andriykohut/meshtastic-e22-node/hardware/kicad/meshtastic-node.kicad_sch

## KiCad design hardware/kicad/meshtastic-node.kicad_sch (2026-08-19)

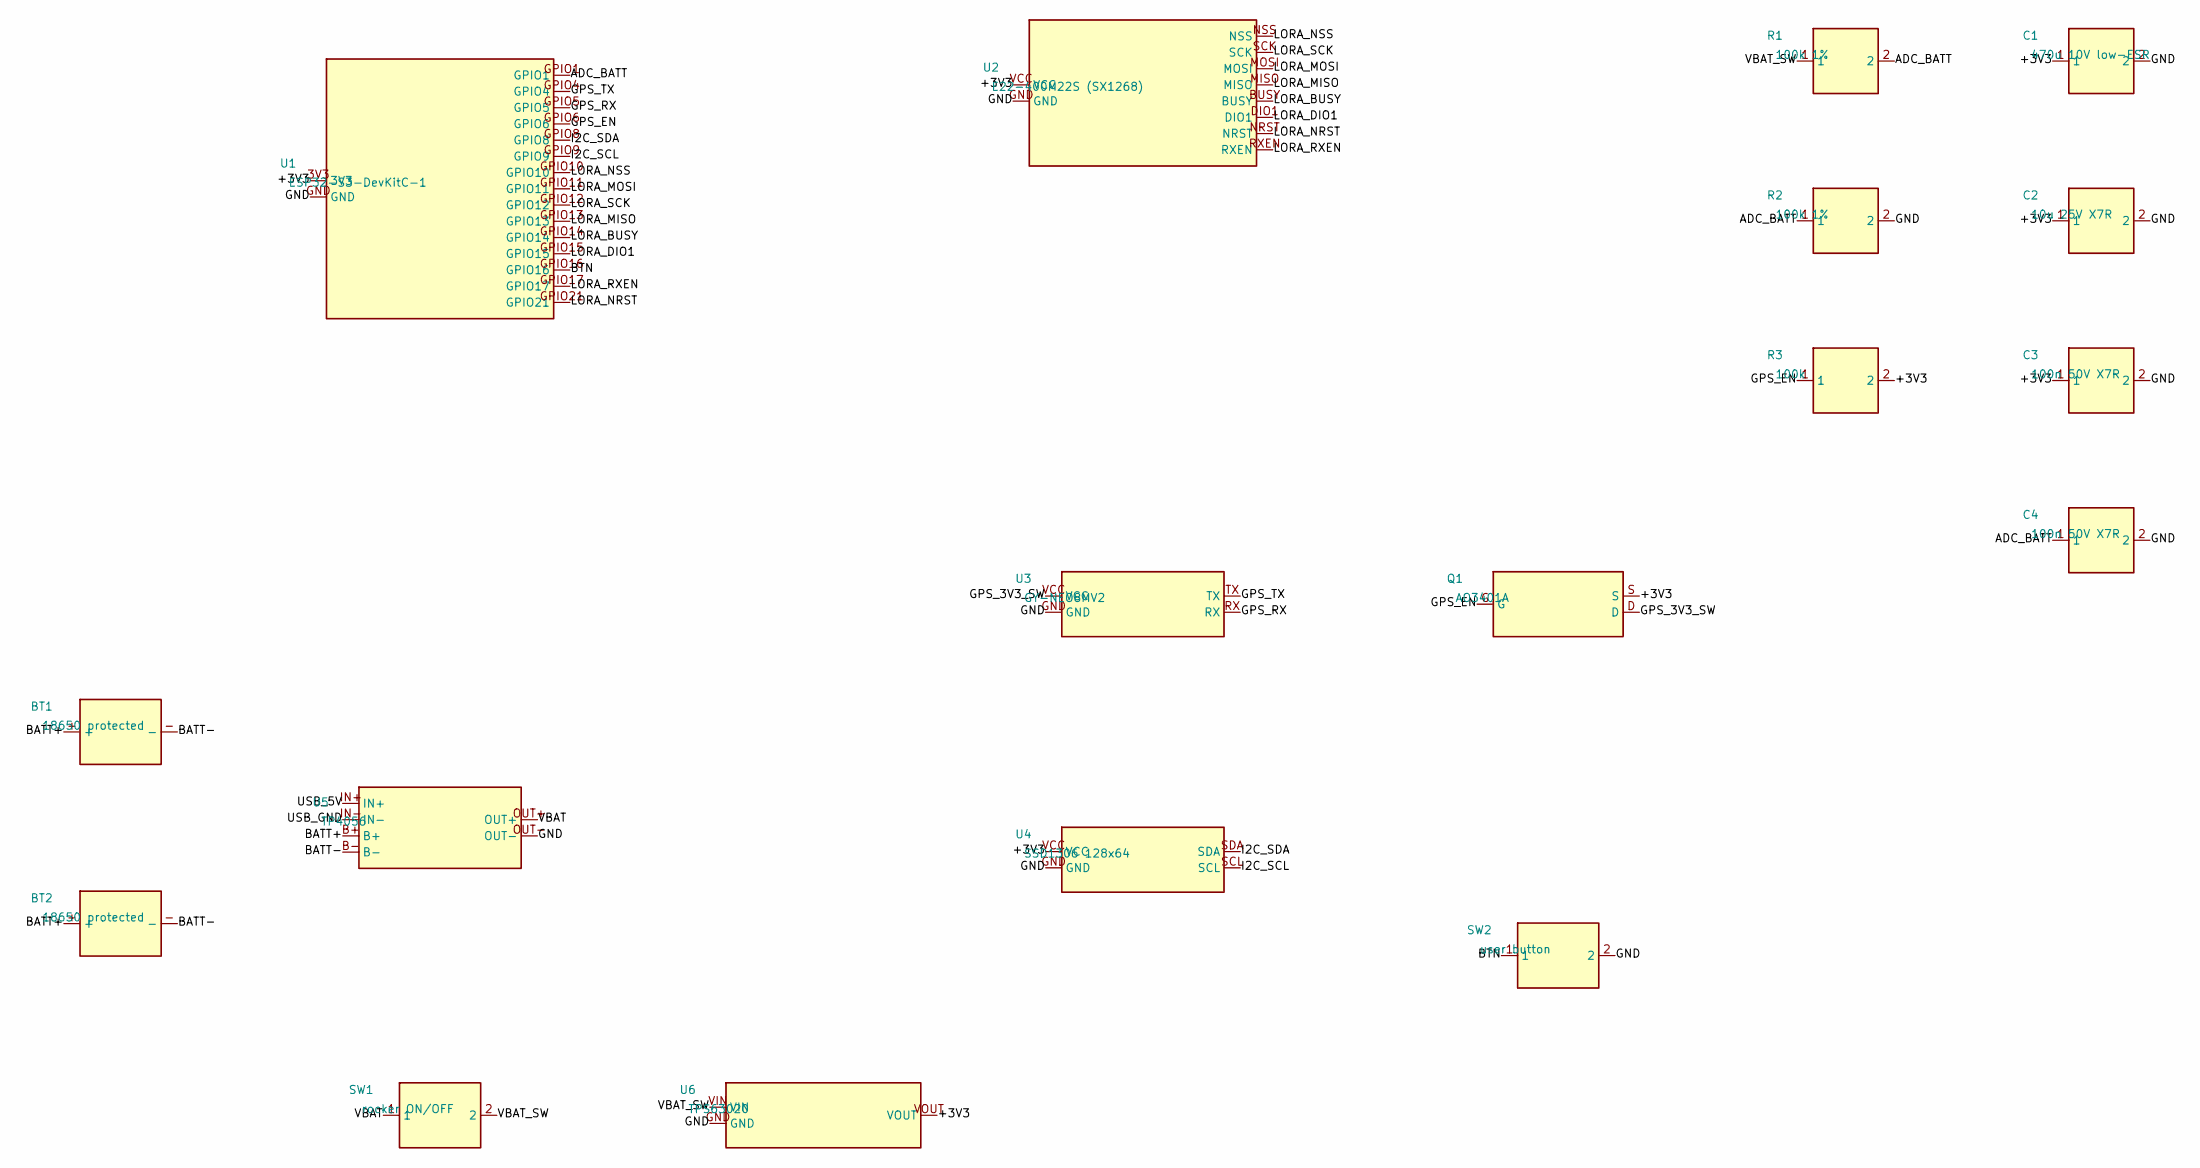
[picture p3: schematic meshtastic-node.kicad_sch]

Parts:
BT1, BT2: 18650 protected
C1: 470u 10V low-ESR
C2: 10u 25V X7R
C3, C4: 100n 50V X7R
Q1: AO3401A
R1, R2: 100k 1%
R3: 100k
SW1: rocker ON/OFF
SW2: user button
U1: ESP32-S3-DevKitC-1
U2: E22-400M22S (SX1268)
U3: GY-NEO8MV2
U4: SSD1306 128x64
U5: TP4056
U6: TPS63020

Connections:
+3V3: C1.1, C2.1, C3.1, Q1.S, R3.2, U1.3V3, U2.VCC, U4.VCC, U6.VOUT
ADC_BATT: C4.1, R1.2, R2.1, U1.GPIO1
BATT+: BT1.+, BT2.+, U5.B+
BATT-: BT1.-, BT2.-, U5.B-
BTN: SW2.1, U1.GPIO16
GND: C1.2, C2.2, C3.2, C4.2, R2.2, SW2.2, U1.GND, U2.GND, U3.GND, U4.GND, U5.OUT-, U6.GND
GPS_3V3_SW: Q1.D, U3.VCC
GPS_EN: Q1.G, R3.1, U1.GPIO6
GPS_RX: U1.GPIO5, U3.RX
GPS_TX: U1.GPIO4, U3.TX
I2C_SCL: U1.GPIO9, U4.SCL
I2C_SDA: U1.GPIO8, U4.SDA
LORA_BUSY: U1.GPIO14, U2.BUSY
LORA_DIO1: U1.GPIO15, U2.DIO1
LORA_MISO: U1.GPIO13, U2.MISO
LORA_MOSI: U1.GPIO11, U2.MOSI
LORA_NRST: U1.GPIO21, U2.NRST
LORA_NSS: U1.GPIO10, U2.NSS
LORA_RXEN: U1.GPIO17, U2.RXEN
LORA_SCK: U1.GPIO12, U2.SCK
USB_5V: U5.IN+
USB_GND: U5.IN-
VBAT: SW1.1, U5.OUT+
VBAT_SW: R1.1, SW1.2, U6.VIN
